maniakm/TeraDMX/PCB v1.2/PNG/TOP.png

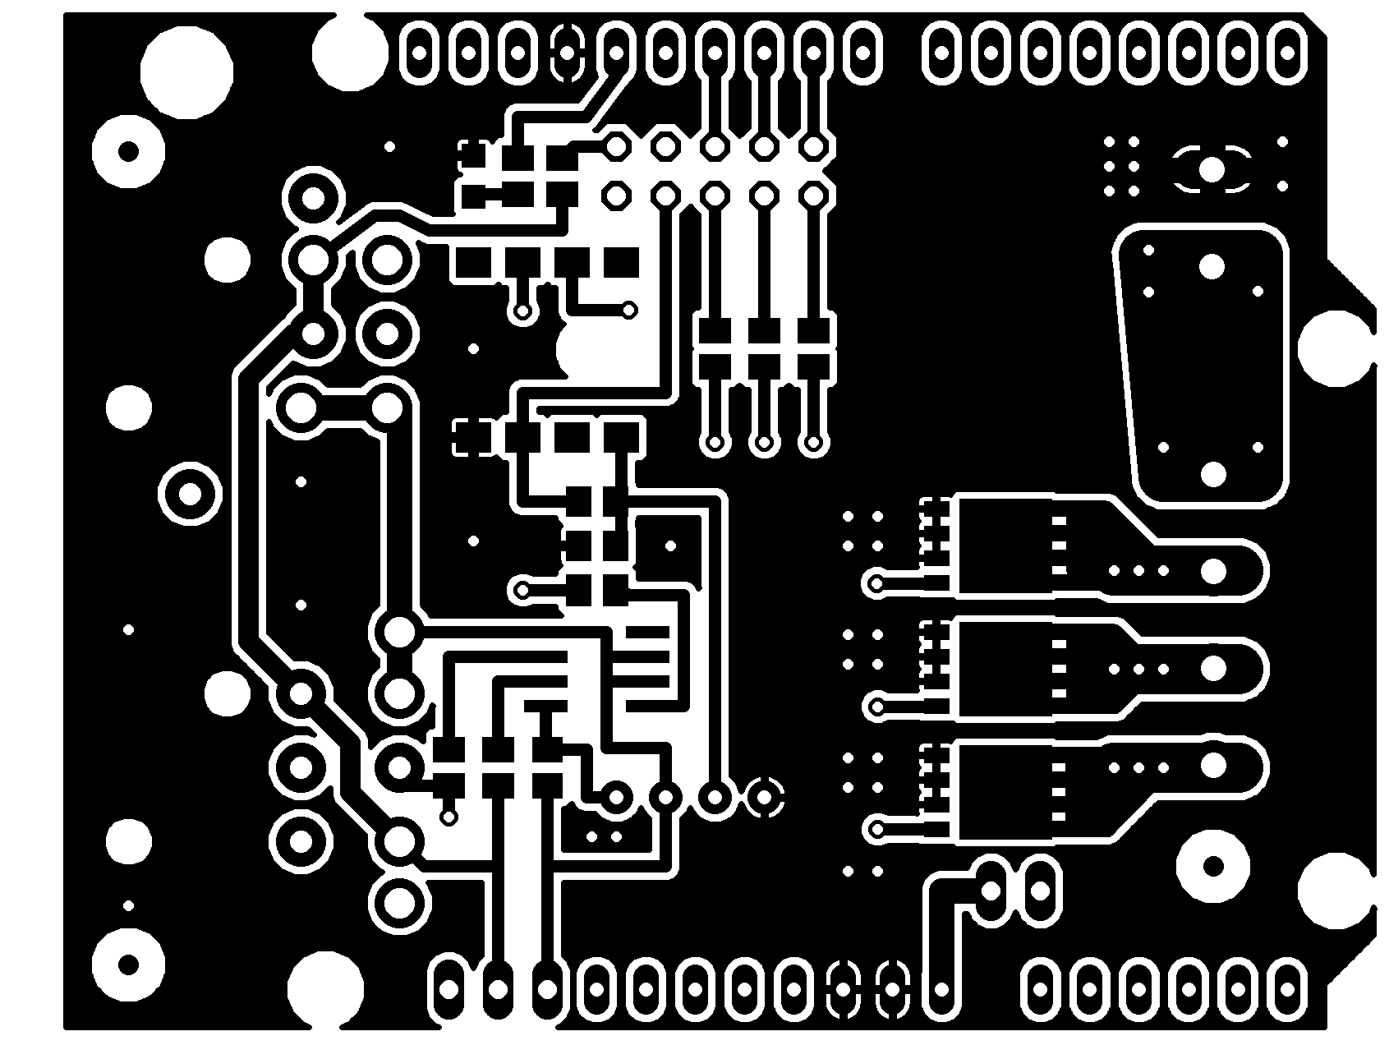
PCB v1.2/PNG/TOP.png
