maniakm/TeraDMX/PCB v1.2/PNG/TOP_BOTTOM.png

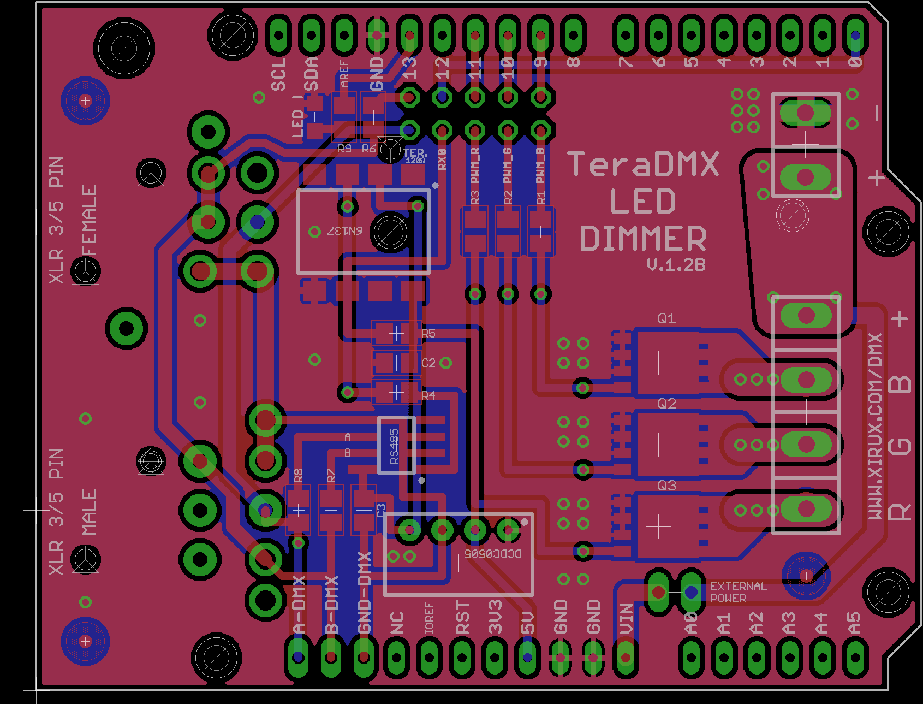
PCB v1.2/PNG/TOP_BOTTOM.png
